ikrishagarwal/Air75/Firmware/rmk/src/bongocat_frames.rs

// Dimensions of the embedded artwork, independent of the OLED configuration.
pub const FRAME_WIDTH: usize = 128;
pub const FRAME_HEIGHT: usize = 32;
pub const FRAME_SIZE: usize = FRAME_WIDTH * FRAME_HEIGHT / 8;

pub const IDLE_FRAMES: [[u8; FRAME_SIZE]; 5] = [
    [
        0x00, 0x00, 0x00, 0x00, 0x00, 0x00, 0xE0, 0xCE, 0x9C, 0xF8, 0xFC, 0xFE, 0x80, 0xE0, 0x20,
        0x00, 0x00, 0x00, 0x00, 0x00, 0x00, 0x00, 0x00, 0x00, 0x00, 0x00, 0x00, 0x00, 0x00, 0x00,
        0x00, 0x00, 0x00, 0x00, 0x00, 0x00, 0x00, 0x00, 0x00, 0x00, 0x00, 0x80, 0x80, 0xC0, 0xC0,
        0xE0, 0xE0, 0xF0, 0xF8, 0xFC, 0xFE, 0xFF, 0xFE, 0xFC, 0xF8, 0xE0, 0xE0, 0xE0, 0xE0, 0xE0,
        0xC0, 0xC0, 0xC0, 0x80, 0x80, 0x00, 0x00, 0x00, 0x00, 0x00, 0x00, 0x00, 0x00, 0x00, 0x00,
        0x00, 0x00, 0x00, 0x00, 0x00, 0x00, 0x00, 0x00, 0x00, 0x00, 0x00, 0x00, 0x00, 0x00, 0x00,
        0x00, 0x00, 0x00, 0x00, 0x00, 0x00, 0x00, 0x00, 0x00, 0x00, 0x00, 0x00, 0x00, 0x00, 0x00,
        0x00, 0x00, 0x00, 0x00, 0x00, 0x00, 0x00, 0x00, 0x00, 0x00, 0x00, 0x00, 0x00, 0x00, 0x00,
        0x00, 0x00, 0x00, 0x00, 0x00, 0x00, 0x00, 0x00, 0x01, 0x01, 0x01, 0x01, 0x02, 0x02, 0x38,
        0xF7, 0xF7, 0xF7, 0xF7, 0xF7, 0xF7, 0x31, 0x00, 0x08, 0x10, 0x10, 0x10, 0x10, 0x20, 0x20,
        0x20, 0x20, 0x40, 0x40, 0x40, 0x40, 0x80, 0x80, 0x80, 0x80, 0xC0, 0xE0, 0xF0, 0xF8, 0xF8,
        0xFC, 0xFC, 0xFE, 0xFF, 0xFF, 0xFF, 0xFF, 0xFF, 0xCF, 0xCF, 0xFF, 0xFF, 0xBF, 0x7F, 0x7F,
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
        0x00, 0x00, 0x00, 0x00, 0x00, 0x00, 0x00, 0x00, 0x00, 0x00, 0x00, 0x00, 0x00, 0x00, 0x00,
        0x00, 0x00, 0x00, 0x00, 0x00, 0x00, 0x00, 0x00, 0x00, 0x00, 0x00, 0x00, 0x00, 0x00, 0x00,
        0x00, 0x00, 0x00, 0x00, 0x00, 0x00, 0x00, 0x00, 0x00, 0x00, 0x00, 0x00, 0x00, 0x80, 0xC0,
        0x60, 0x30, 0x10, 0x18, 0x08, 0x08, 0x08, 0x18, 0x10, 0x30, 0x60, 0x40, 0xC0, 0x86, 0x87,
        0x85, 0xC4, 0x49, 0x69, 0x3E, 0x0E, 0x13, 0x11, 0x12, 0x12, 0x3D, 0x2D, 0x25, 0x26, 0x44,
        0x68, 0x78, 0x58, 0x9D, 0x97, 0x93, 0xE3, 0x62, 0x34, 0x3C, 0x2C, 0x26, 0xC7, 0xC5, 0x69,
        0x39, 0x19, 0x1D, 0x36, 0xA2, 0xE2, 0x62, 0x34, 0x3C, 0x2C, 0x44, 0xC8, 0xC8, 0xE9, 0xB9,
        0x11, 0x11, 0x13, 0x93, 0xE3, 0x63, 0x27, 0x27, 0x47, 0x47, 0xCF, 0xCF, 0x0F, 0x08, 0x10,
        0x10, 0x10, 0x10, 0x20, 0x20, 0x20, 0x20, 0x40, 0x40, 0x40, 0x40, 0x80, 0x80, 0x80, 0x80,
        0x00, 0x00, 0x00, 0x00, 0x00, 0x00, 0x00, 0x00, 0x00, 0x00, 0x00, 0x00, 0x00, 0x00, 0x00,
        0x00, 0x00, 0x00, 0x00, 0x00, 0x00, 0x00, 0x00, 0x00, 0x00, 0x00, 0x00, 0x00, 0x00, 0x00,
        0x00, 0x00,
    ],
];
